RegionallyFamous/swansong-usb/review-renders/top-rev-c.png

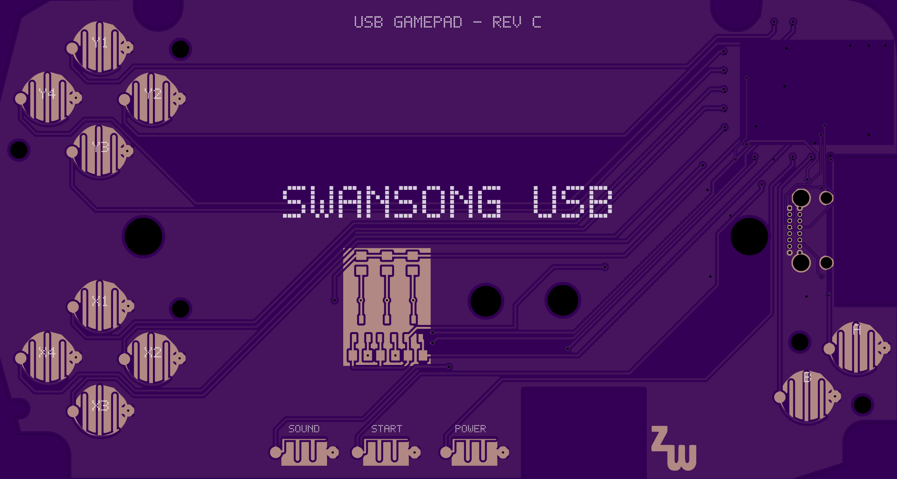
review-renders/top-rev-c.png
